dynamicalsystemslaboratory/opennest/.photos/20251110_133927.jpg

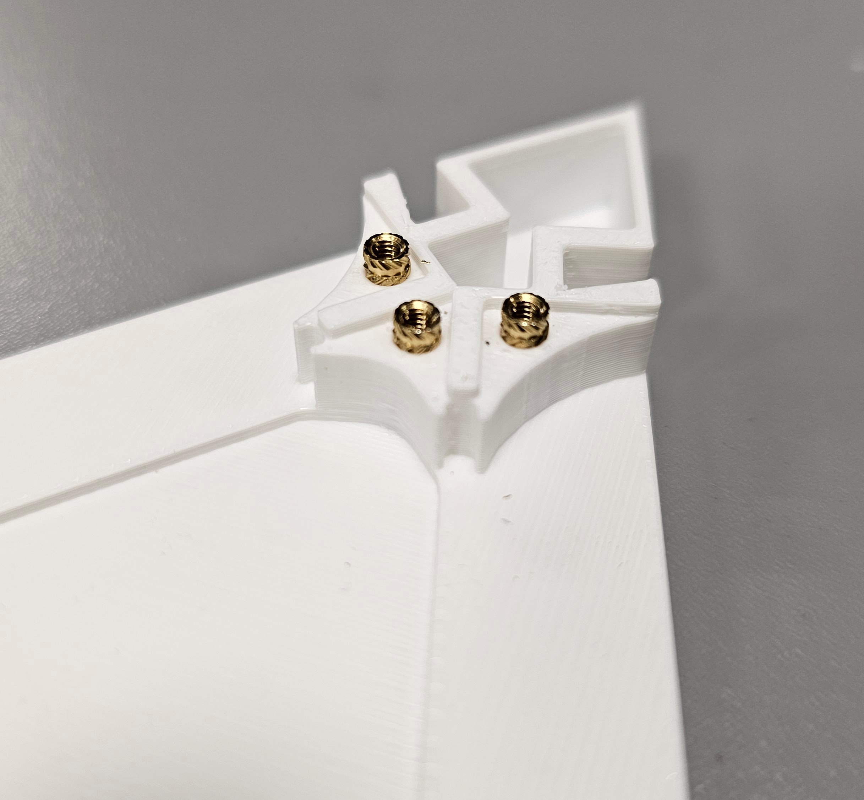
.photos/20251110_133927.jpg
