dynamicalsystemslaboratory/opennest/.photos/20251110_134035.jpg

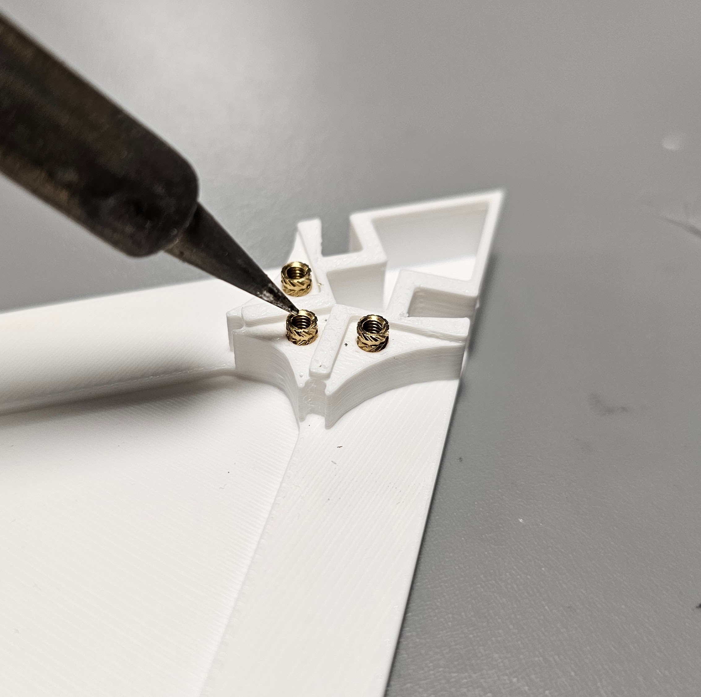
.photos/20251110_134035.jpg
