dynamicalsystemslaboratory/opennest/.photos/20251110_134107.jpg

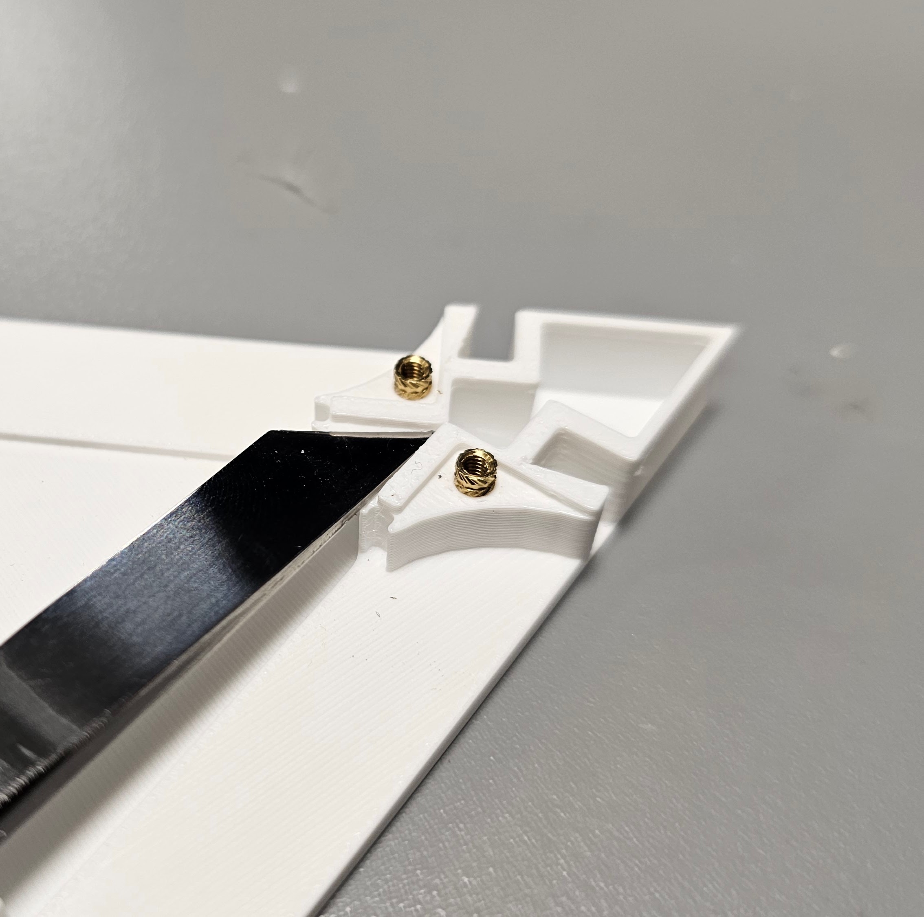
.photos/20251110_134107.jpg
