dynamicalsystemslaboratory/opennest/.photos/20251110_134204.jpg

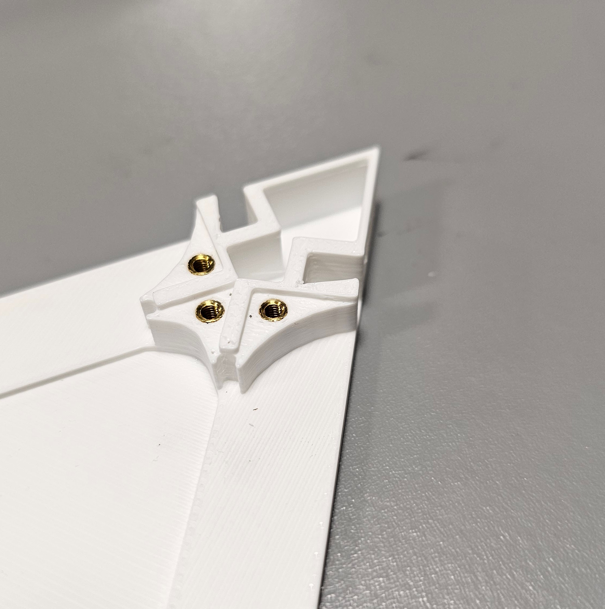
.photos/20251110_134204.jpg
