dynamicalsystemslaboratory/opennest/.photos/20251110_151157.jpg

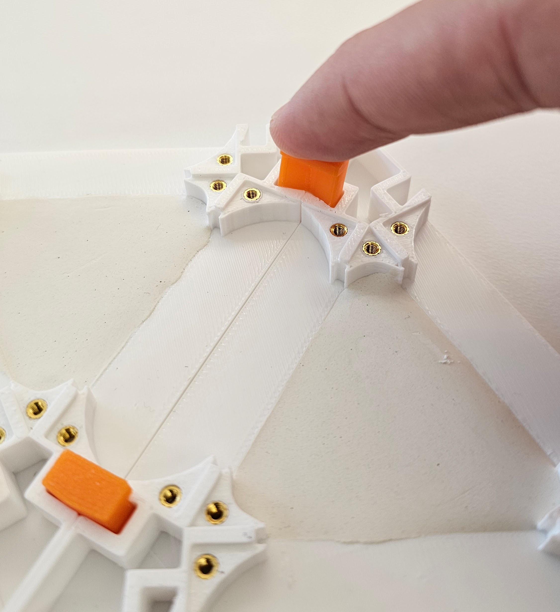
.photos/20251110_151157.jpg
