dynamicalsystemslaboratory/opennest/.photos/20251110_151159.jpg

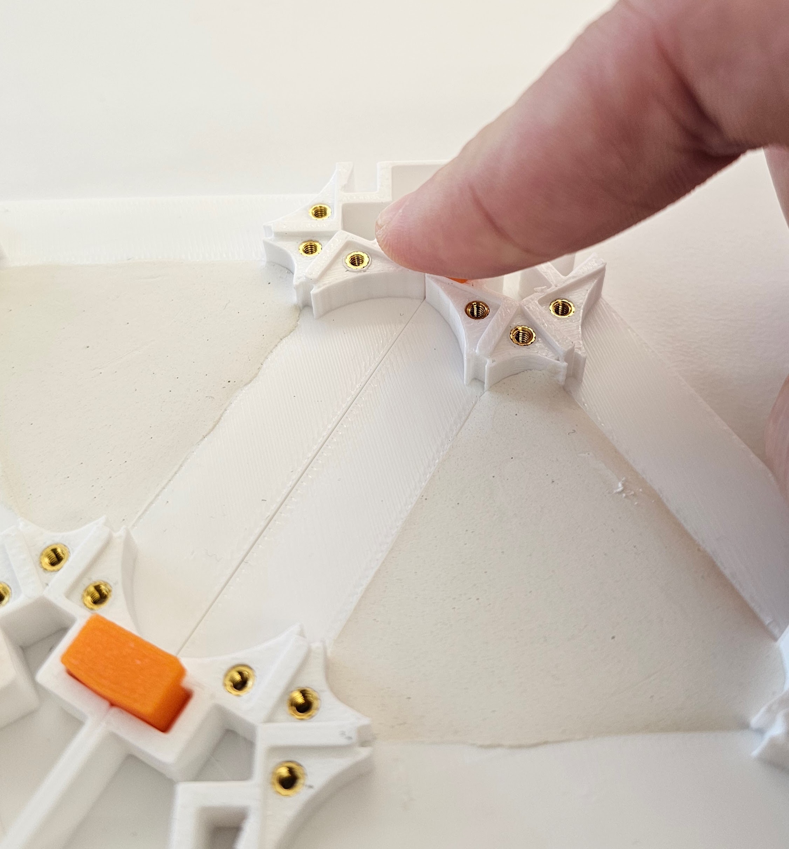
.photos/20251110_151159.jpg
