dynamicalsystemslaboratory/opennest/.photos/20251110_151228.jpg

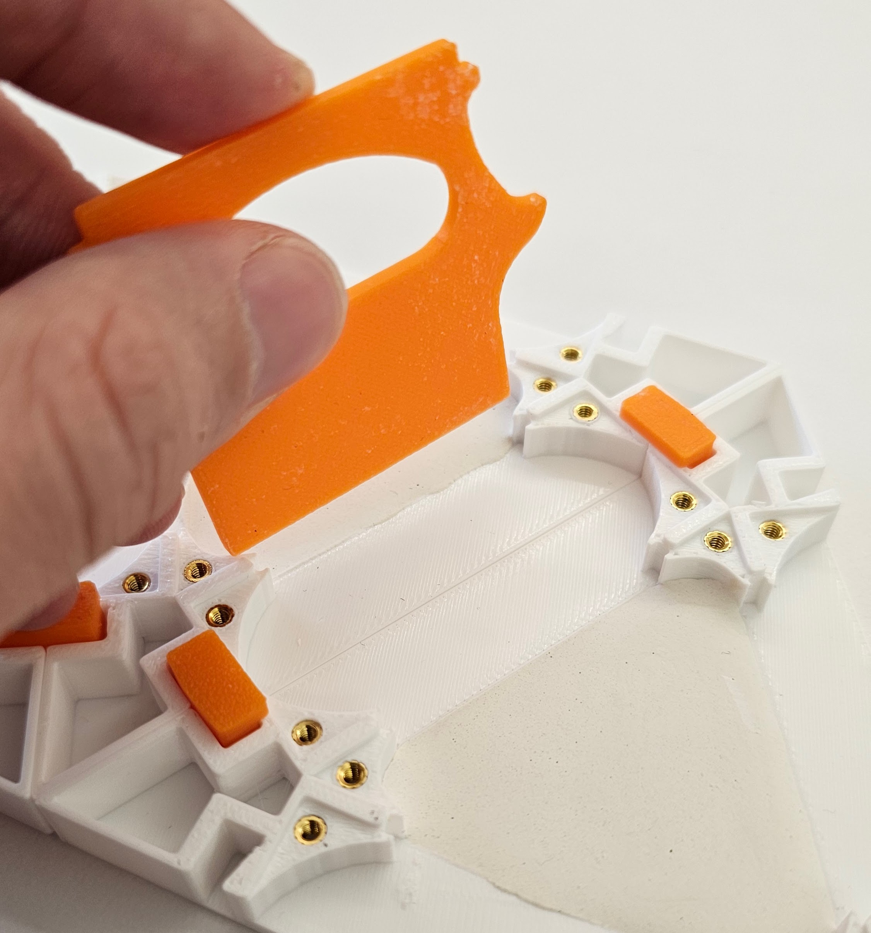
.photos/20251110_151228.jpg
