dynamicalsystemslaboratory/opennest/.photos/20251110_151242.jpg

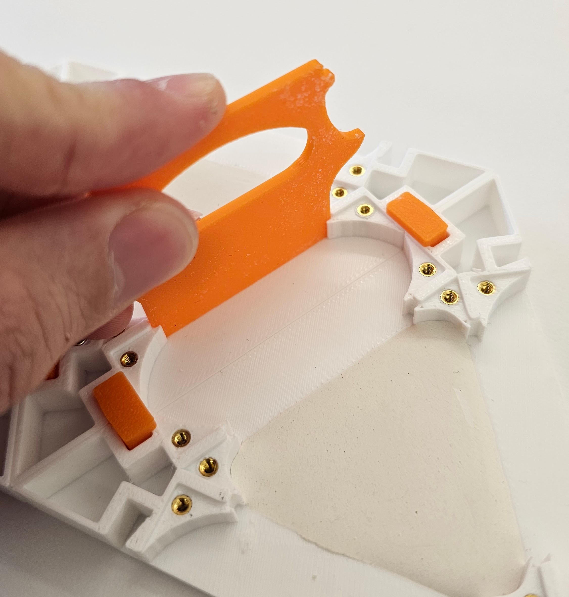
.photos/20251110_151242.jpg
